MoeezMufti/SS26_HWE_Lab_Team_A8/8-BIT_CPU/VHDL/Component Schematics/program_counter_schematic.pdf

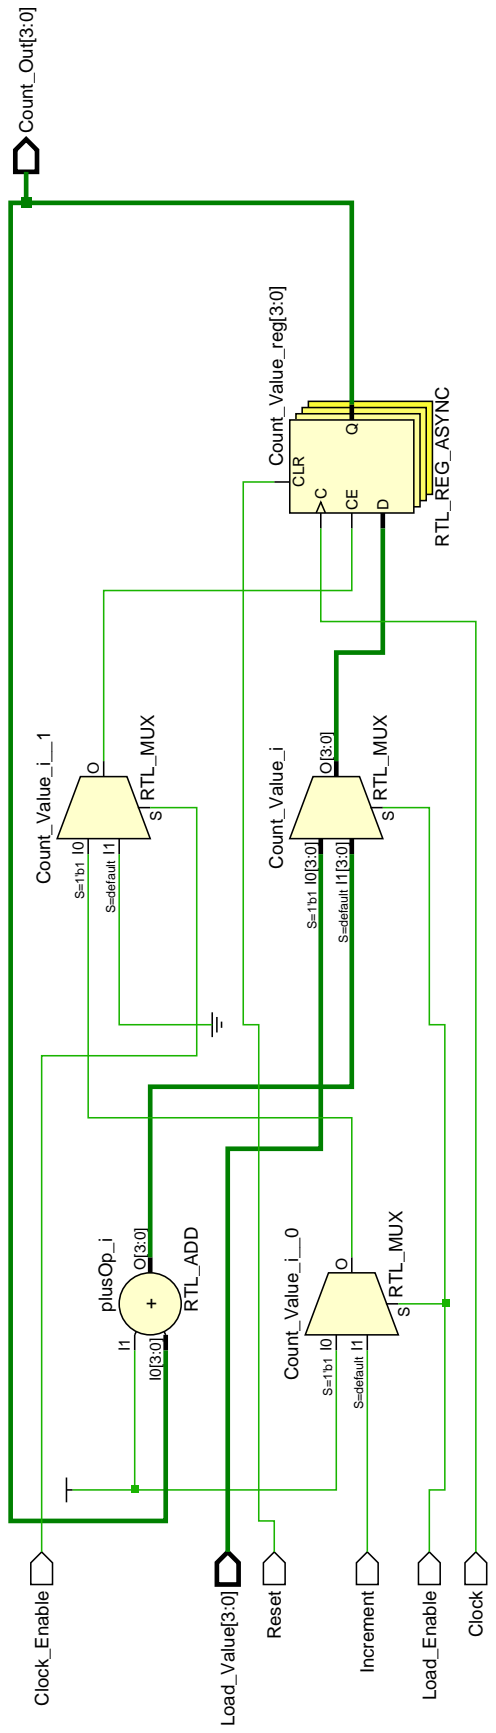
[picture p44: figure]
Clock_Enable; Load_Value[3:0]; Reset; Increment; Load_Enable; Clock; plusOp_i +; RTL_ADD; Count_Value_i__0; RTL_MUX; I1 S=default; Count_Value_i__1; Count_Value_i; I1[3:0] S=default; Count_Value_reg[3:0]; RTL_REG_ASYNC C; CLR; Count_Out[3:0]
