MoeezMufti/SS26_HWE_Lab_Team_A8/8-BIT_CPU/VHDL/Component Schematics/memory_schematic.pdf

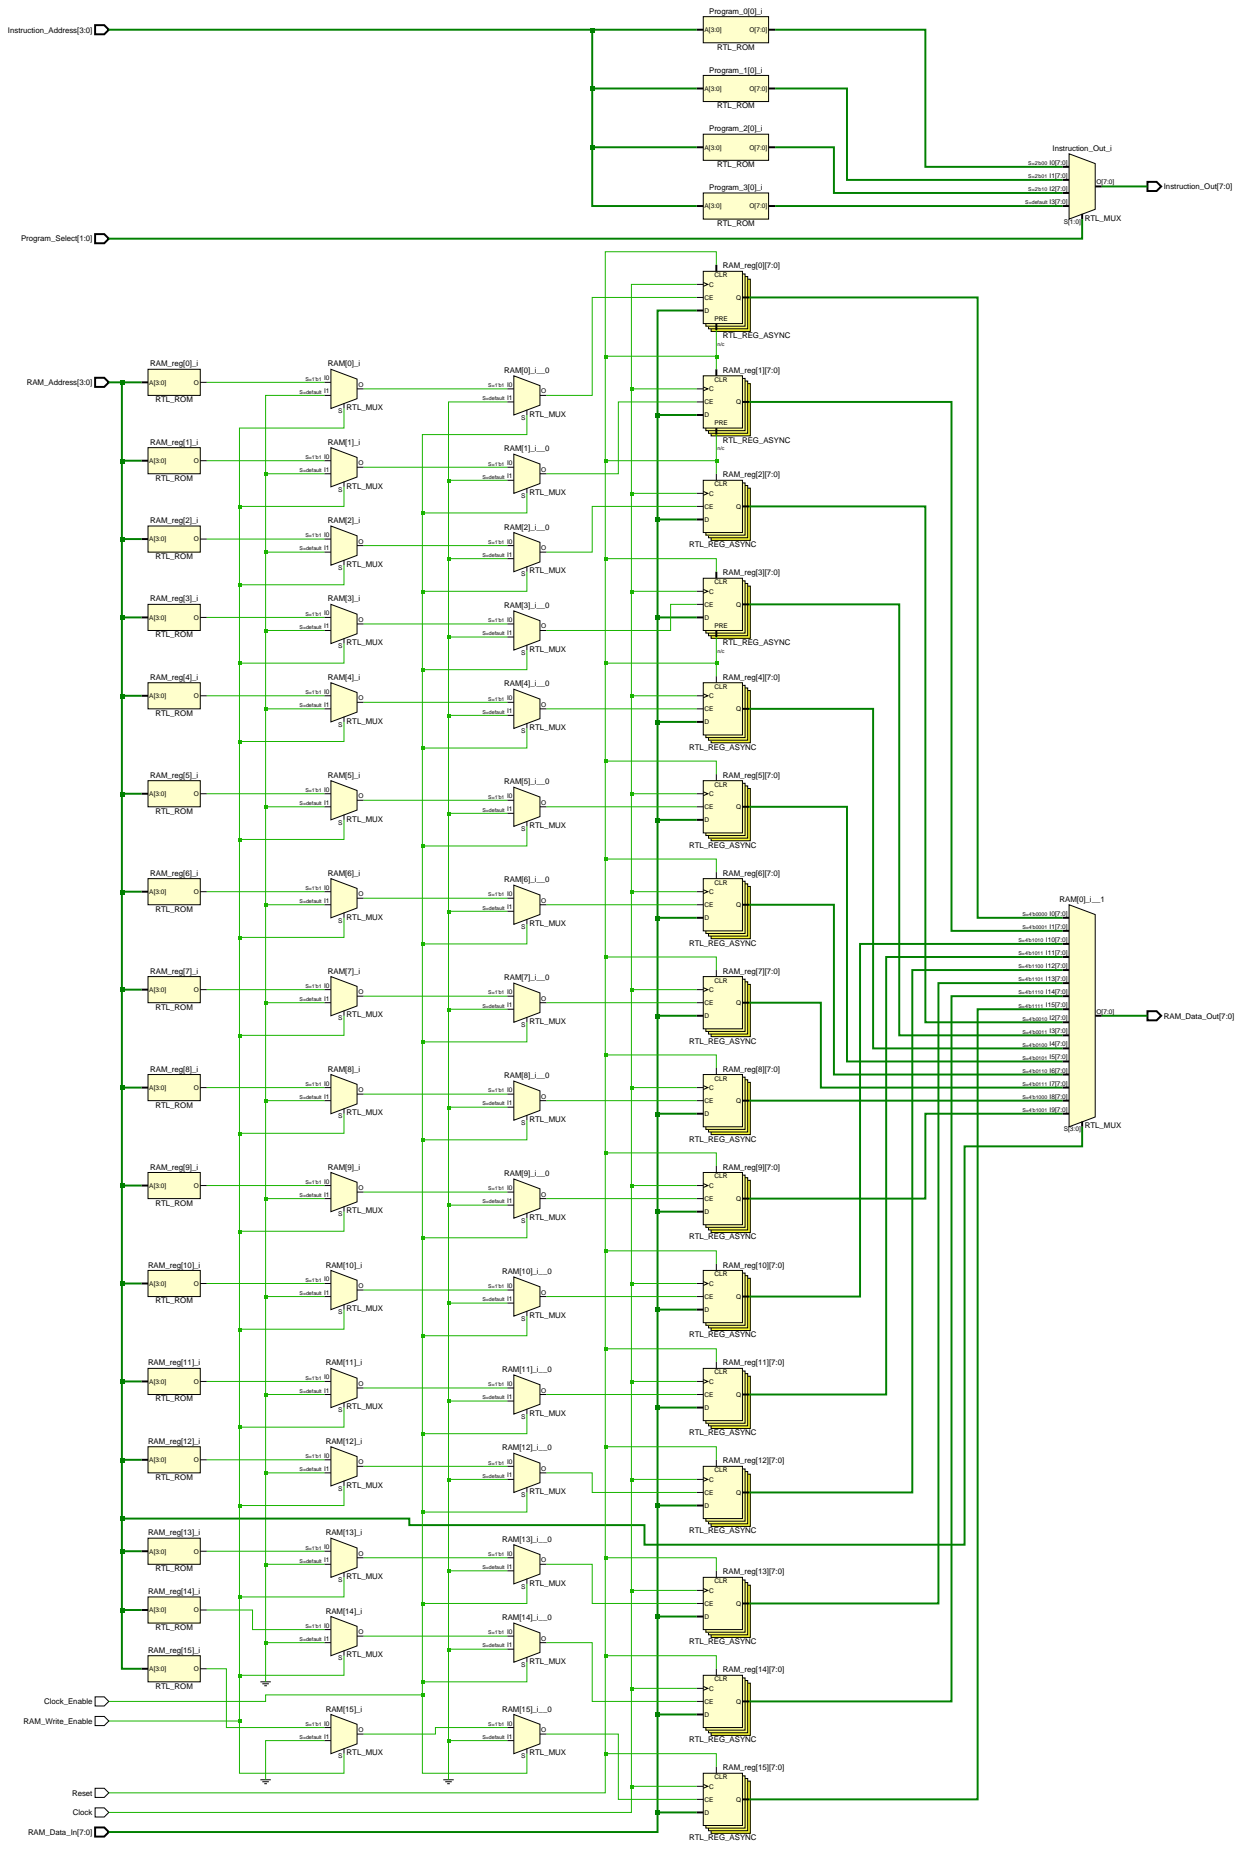
[picture p59: page 1]
Instruction_Address[3:0]; Program_Select[1:0]; RAM_Address[3:0]; Clock_Enable; RAM_Write_Enable; Reset; Clock; RAM_Data_In[7:0]; RAM_reg[0]_i; RTL_ROM; RAM_reg[1]_i; RAM_reg[2]_i; RAM_reg[3]_i; RAM_reg[4]_i; RAM_reg[5]_i; RAM_reg[6]_i; RAM_reg[7]_i; RAM_reg[8]_i; RAM_reg[9]_i; RAM_reg[10]_i; RAM_reg[11]_i; RAM_reg[12]_i; RAM_reg[13]_i; RAM_reg[14]_i; RAM_reg[15]_i; RAM[0]_i; RTL_MUX; S=default I1; RAM[1]_i; RAM[2]_i; RAM[3]_i; RAM[4]_i; RAM[5]_i; RAM[6]_i; RAM[7]_i; RAM[8]_i; RAM[9]_i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
