MoeezMufti/SS26_HWE_Lab_Team_A8/Exercise Files/Lab 05 - Introduction to FPGA Design/src/switch_led_bitvector.vhd

----------------------------------------------------------------------------------
-- Company: 
-- Engineer: 
-- 
-- Create Date: 06/30/2026 01:25:23 PM
-- Design Name: 
-- Module Name: switch_led_bitvector - Behavioral
-- Project Name: 
-- Target Devices: 
-- Tool Versions: 
-- Description: 
-- 
-- Dependencies: 
-- 
-- Revision:
-- Revision 0.01 - File Created
-- Additional Comments:
-- 
----------------------------------------------------------------------------------


library IEEE;
use IEEE.STD_LOGIC_1164.ALL;

-- Uncomment the following library declaration if using
-- arithmetic functions with Signed or Unsigned values
--use IEEE.NUMERIC_STD.ALL;

-- Uncomment the following library declaration if instantiating
-- any Xilinx leaf cells in this code.
--library UNISIM;
--use UNISIM.VComponents.all;

entity switch_led_bitvector is
--  Port ( );
end switch_led_bitvector;

architecture Behavioral of switch_led_bitvector is

begin


end Behavioral;
